manoranjan2050/ESP32-AC-Energy-Monitor/hardware/renders/final_6ct_preview.png

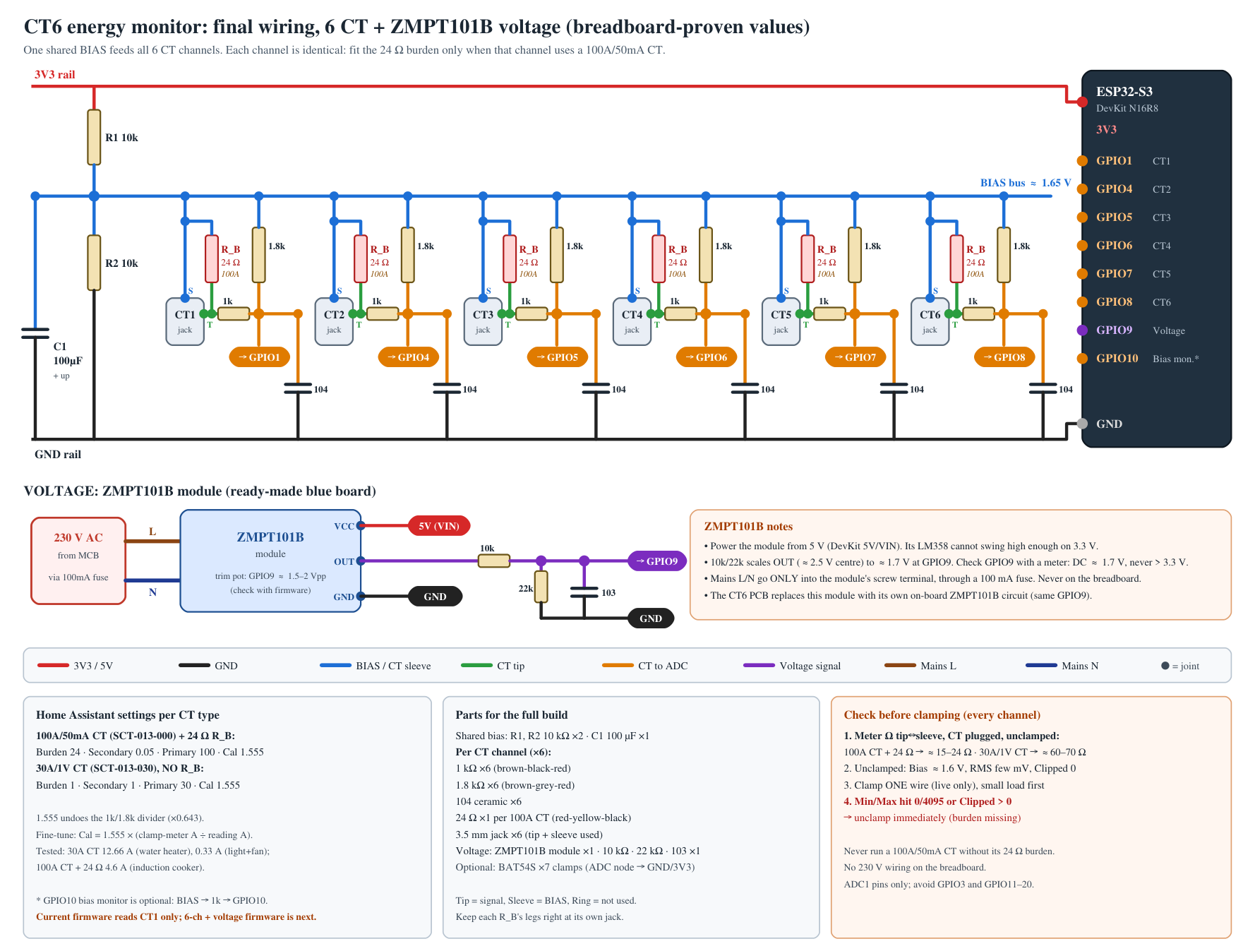
hardware/renders/final_6ct_preview.png
