manoranjan2050/ESP32-AC-Energy-Monitor/hardware/renders/easyeda_guide_preview.png

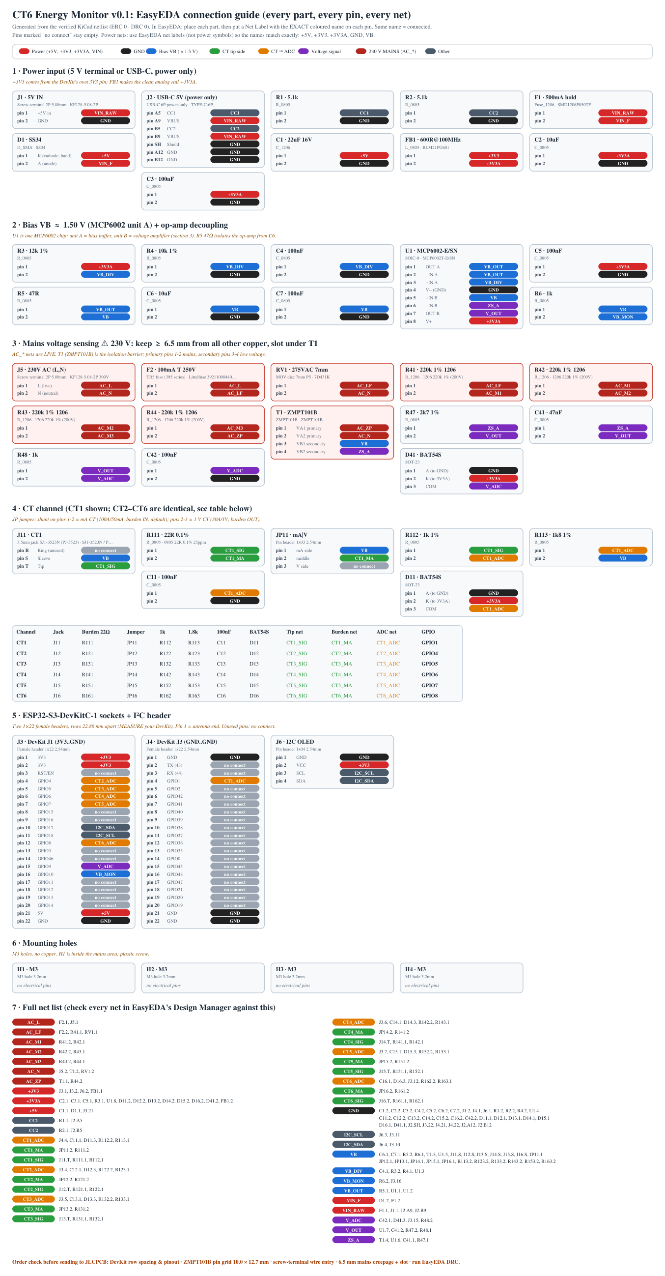
hardware/renders/easyeda_guide_preview.png
